7emoutyX/stm32dev_board/Final results/55.png

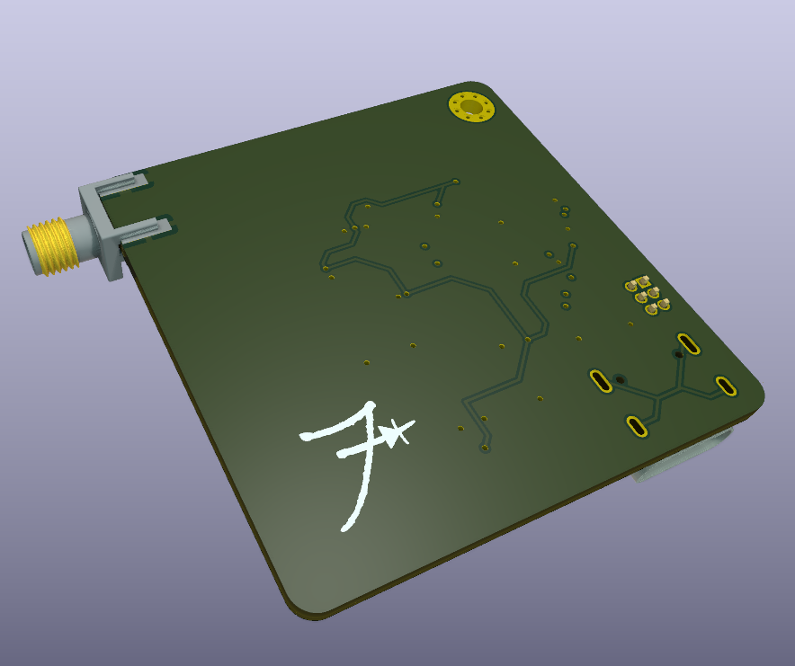
Final results/55.png
